Scrath1/ESPlanter/circuit_diagram/circuit_diagram.kicad_sch

## KiCad design circuit_diagram/circuit_diagram.kicad_sch (2025-04-09)

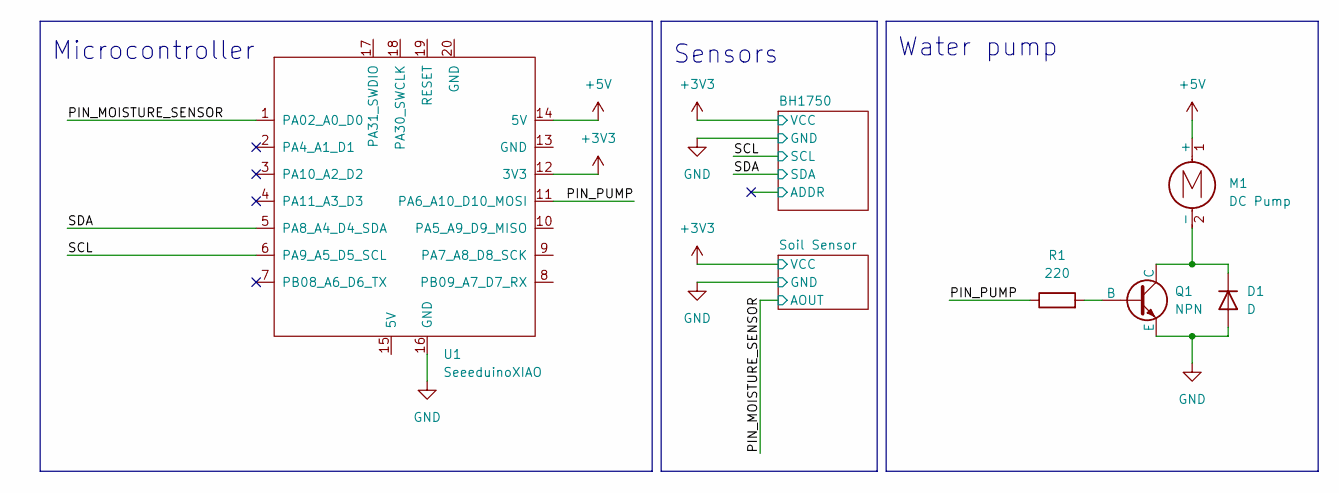
[picture p3: schematic circuit_diagram.kicad_sch]

Parts:
D1: D
M1: DC Pump
Q1: NPN
R1: 220
U1: SeeeduinoXIAO

Connections:
+3V3: U1.12 (3V3)
+5V: M1.1 (+), U1.14 (5V)
GND: D1.2 (A), Q1.3 (E), U1.16 (GND)
unnamed: D1.1 (K), M1.2 (-), Q1.1 (C)
unnamed: Q1.2 (B), R1.2
PIN_MOISTURE_SENSOR: U1.1 (PA02_A0_D0)
PIN_PUMP: R1.1, U1.11 (PA6_A10_D10_MOSI)
SCL: U1.6 (PA9_A5_D5_SCL)
SDA: U1.5 (PA8_A4_D4_SDA)

Notes on the sheet:
Water pump
Sensors
Microcontroller
