Scrath1/ESPlanter/include/mqtt_functions.h

#ifndef MQTT_FUNCTIONS_H
#define MQTT_FUNCTIONS_H
#include <MQTT.h>
#include <WiFi.h>

#include "global.h"

extern MQTTClient mqttClient;

/**
 * Runs the MQTT setup process, thereby checking the validity of
 * the configured broker address to determine whether an MQTT connection
 * is desired. If it is, a task for managing the connection is established.
 *
 * This function can be re-run multiple times without issues
 */
void mqtt_setup();

/**
 * Checks whether the MQTT client is still connected.
 * If not, an attempt to reconnect is made.
 * On successful reconnect, topic subscriptions are renewed
 */
void mqtt_maintain_connection();

#endif  // MQTT_FUNCTIONS_H
